aryatajne28/CrystalBoard/take-two/images/1.jpeg

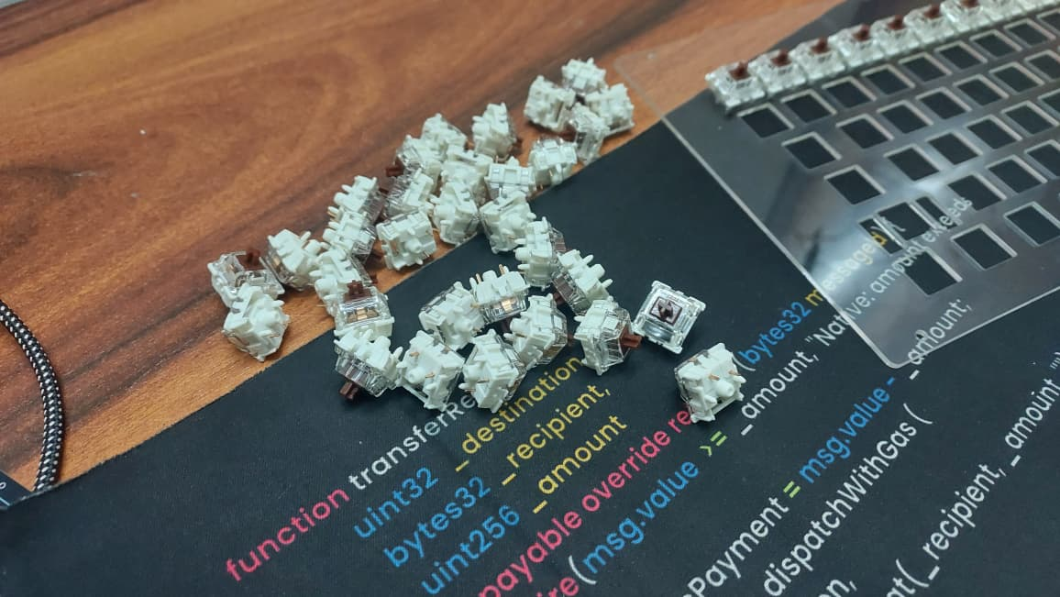
take-two/images/1.jpeg
