aryatajne28/CrystalBoard/take-two/images/2.jpeg

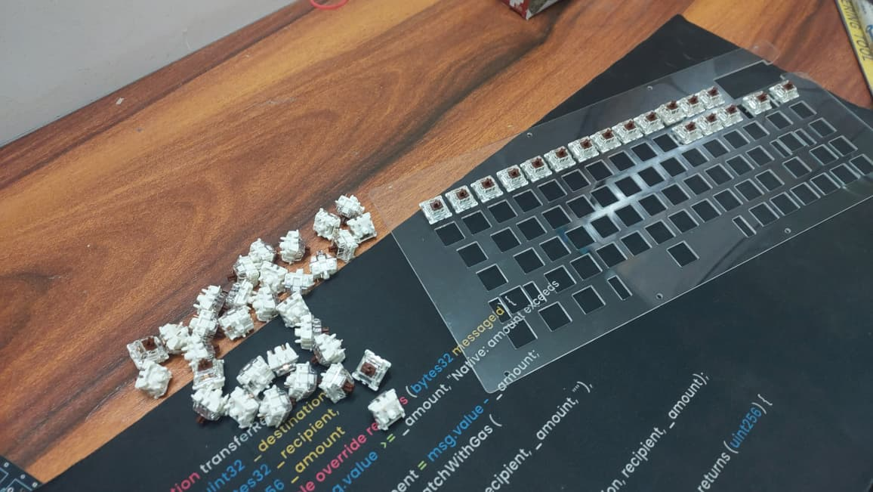
take-two/images/2.jpeg
