aryatajne28/CrystalBoard/take-two/images/3.jpeg

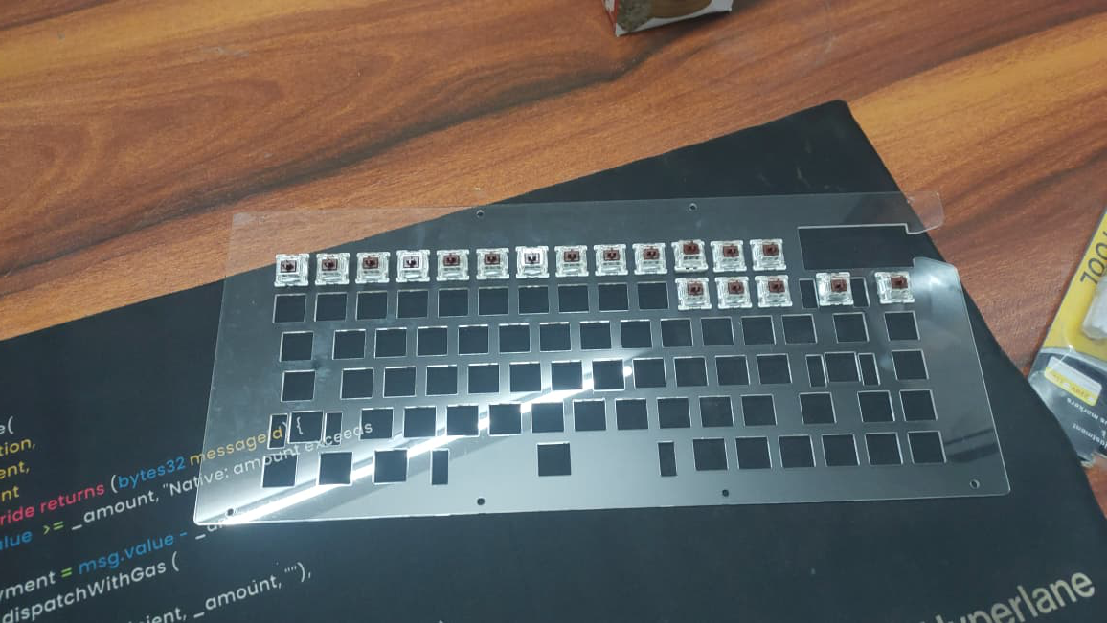
take-two/images/3.jpeg
