aryatajne28/CrystalBoard/take-two/images/4.jpeg

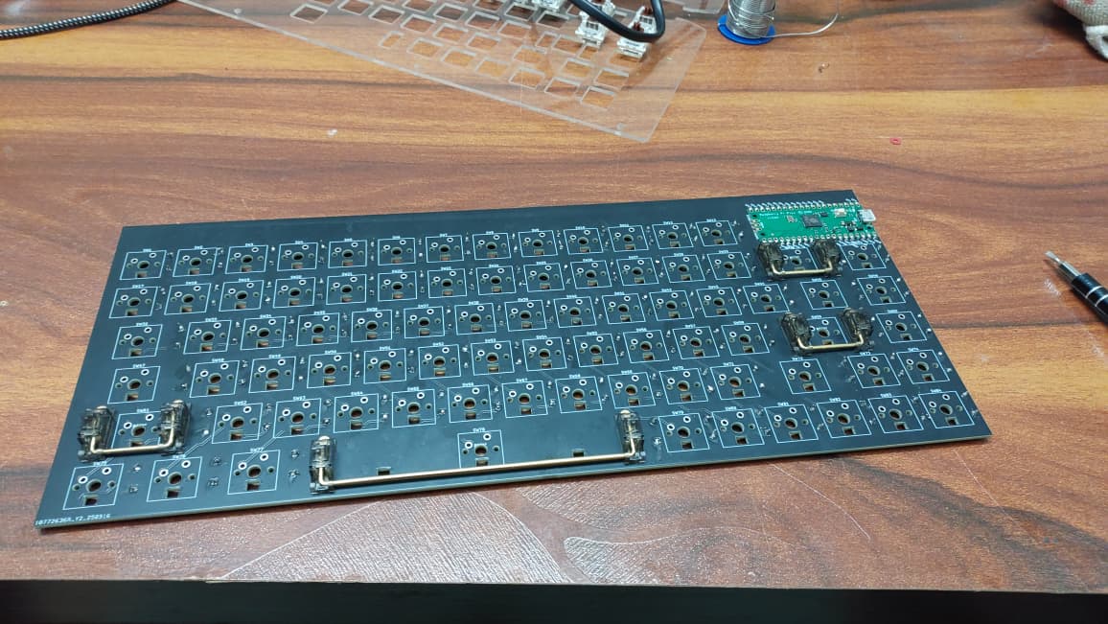
take-two/images/4.jpeg
