aryatajne28/CrystalBoard/take-two/images/5.jpeg

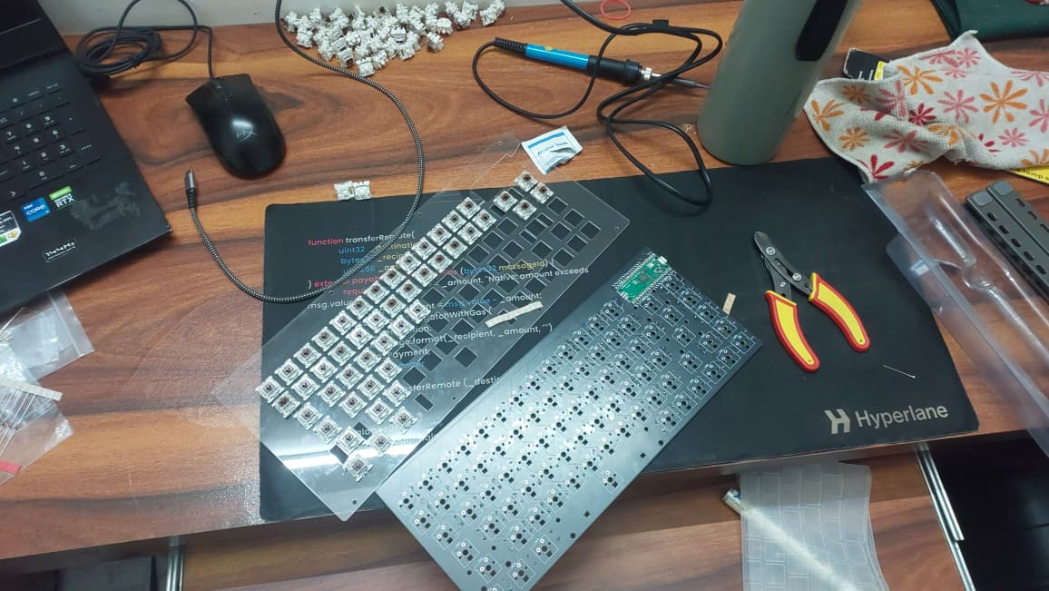
take-two/images/5.jpeg
