aryatajne28/CrystalBoard/take-two/images/6.jpeg

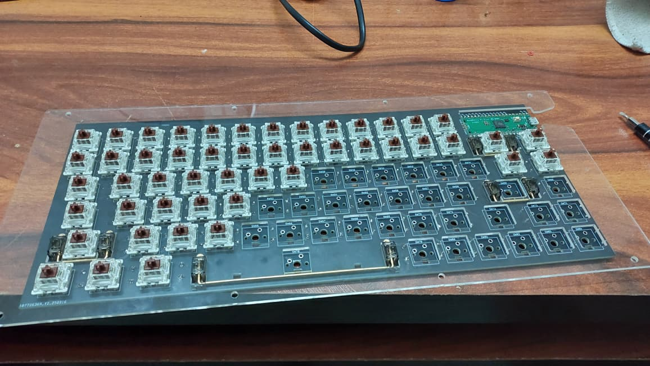
take-two/images/6.jpeg
