aryatajne28/CrystalBoard/take-two/images/7.jpeg

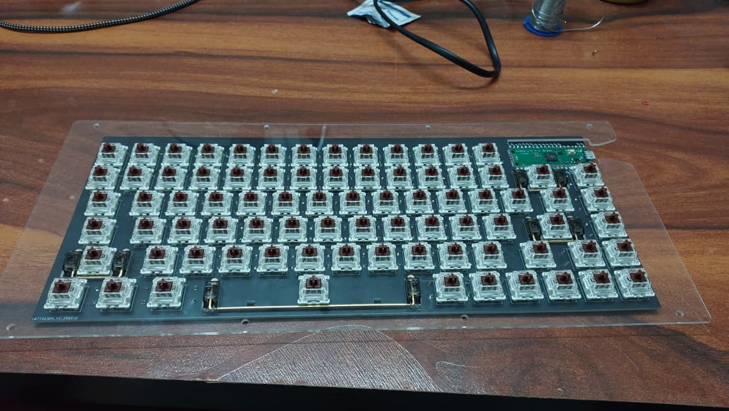
take-two/images/7.jpeg
