aryatajne28/CrystalBoard/take-two/images/8.jpeg

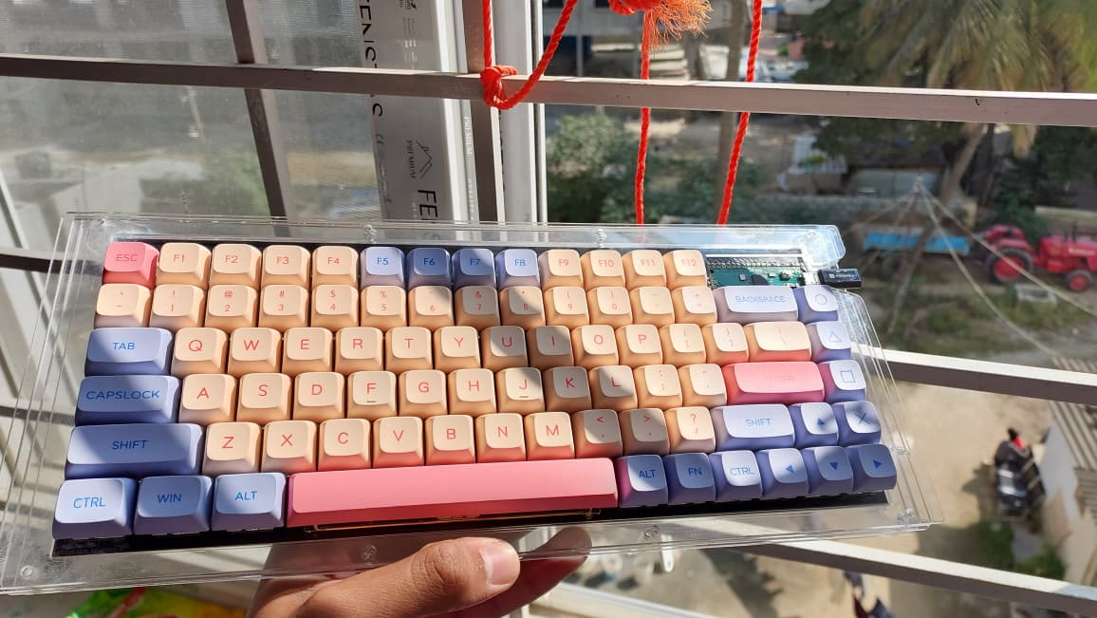
take-two/images/8.jpeg
