aryatajne28/CrystalBoard/take-two/images/9.jpeg

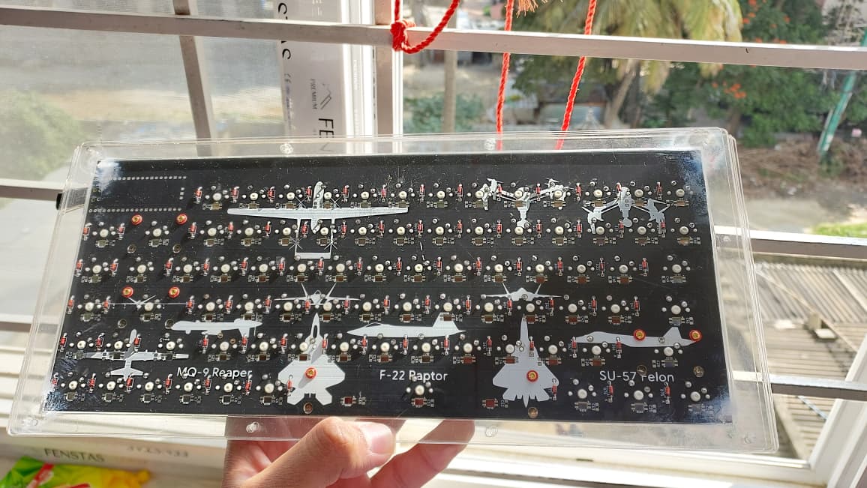
take-two/images/9.jpeg
