aryatajne28/CrystalBoard/take-two/images/10.jpeg

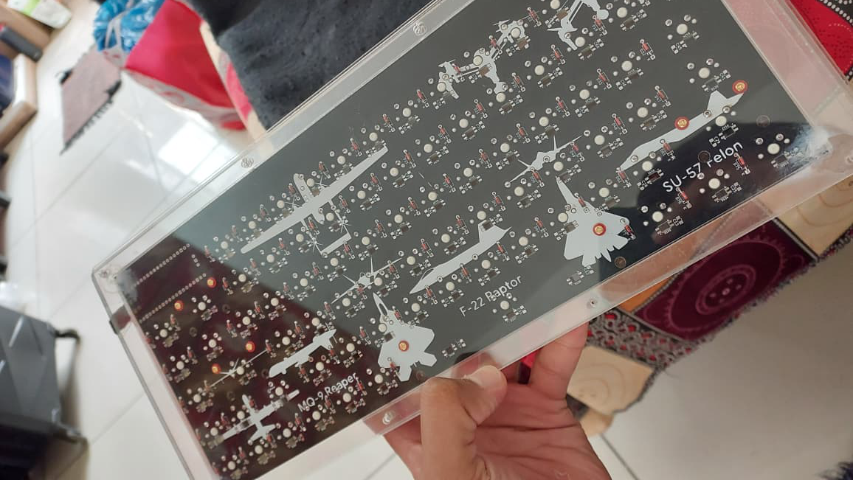
take-two/images/10.jpeg
